krjaskowiak25/T41-SDT-Published/V010 5 in case Stl Files/T41 stand V010-Body.stl

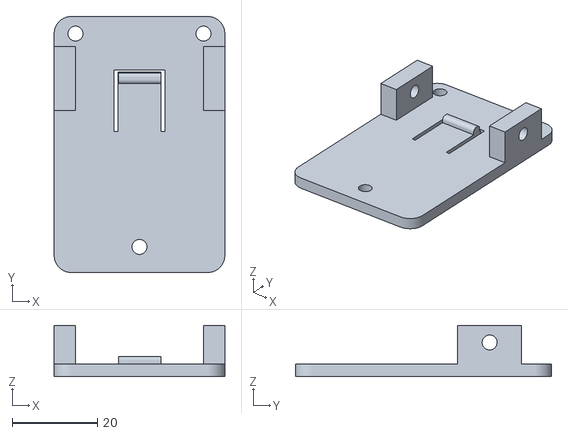
[picture p15: CAD file, 2022-06-29]
V010 5 in case Stl Files/T41 stand V010-Body.stl
40.0 x 60.0 x 12.0
