krjaskowiak25/T41-SDT-Published/V011 7 in case files/T41 7in Side Right Panel V011.FCStd

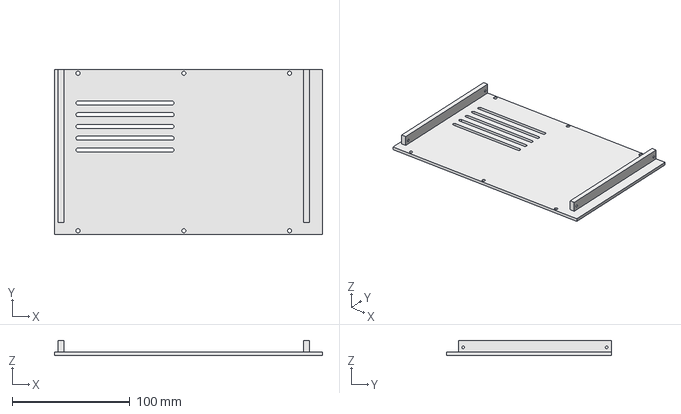
[picture p16: CAD file, 2022-06-29]
V011 7 in case files/T41 7in Side Right Panel V011.FCStd
228.0 x 140.0 x 13.0 mm
