krjaskowiak25/T41-SDT-Published/V011 7 in case files/T41 7in Base Left  V011.FCStd

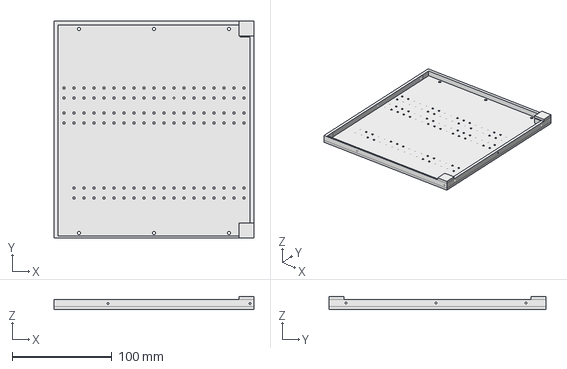
[picture p17: CAD file, 2022-06-29]
V011 7 in case files/T41 7in Base Left V011.FCStd
200.0 x 217.0 x 13.0 mm
