krjaskowiak25/T41-SDT-Published/V010 5 in case FreeCad Files/T41 Back Right Panel V010.FCStd

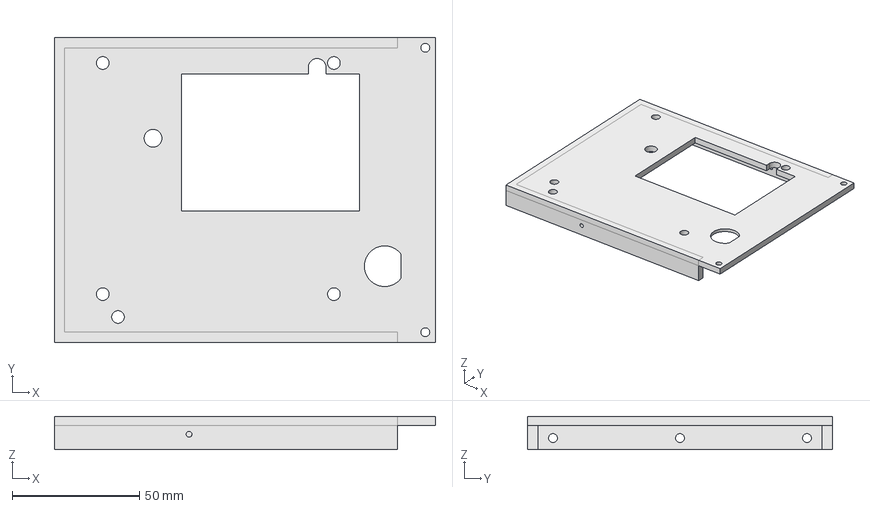
[picture p18: CAD file, 2022-06-29]
V010 5 in case FreeCad Files/T41 Back Right Panel V010.FCStd
150.0 x 120.0 x 13.0 mm
