krjaskowiak25/T41-SDT-Published/V011 7 in case files/T41 7in Front left panelV011.FCStd

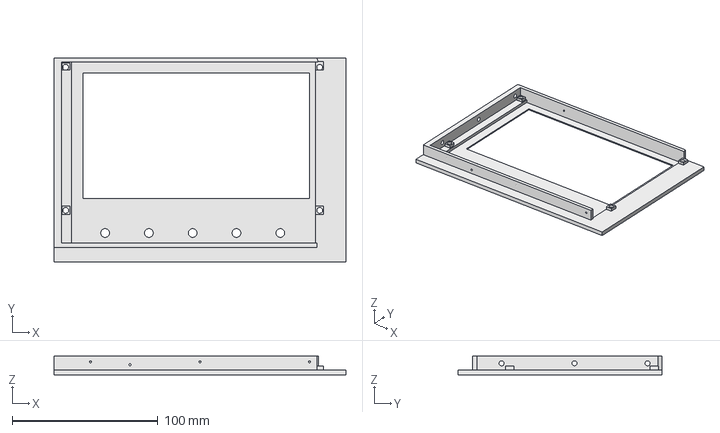
[picture p19: CAD file, 2022-06-29]
V011 7 in case files/T41 7in Front left panelV011.FCStd
200.0 x 140.0 x 13.0 mm
