krjaskowiak25/T41-SDT-Published/V011 7 in case files/T41 7IN Front Right Panel V011.FCStd

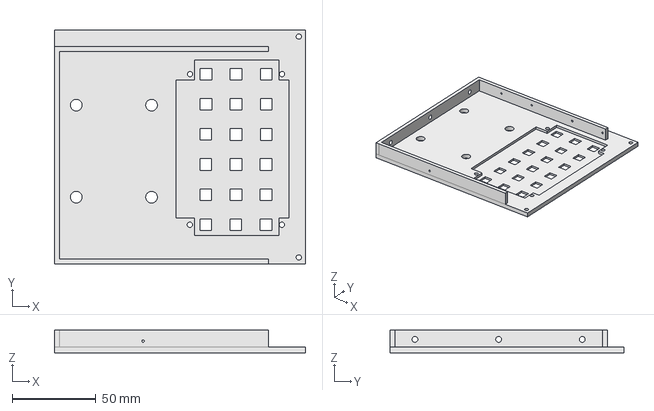
[picture p20: CAD file, 2022-06-29]
V011 7 in case files/T41 7IN Front Right Panel V011.FCStd
150.0 x 140.0 x 13.5 mm
