krjaskowiak25/T41-SDT-Published/V011 7 in case files/T41 7in Top Left Panel Speaker Vents V011.FCStd

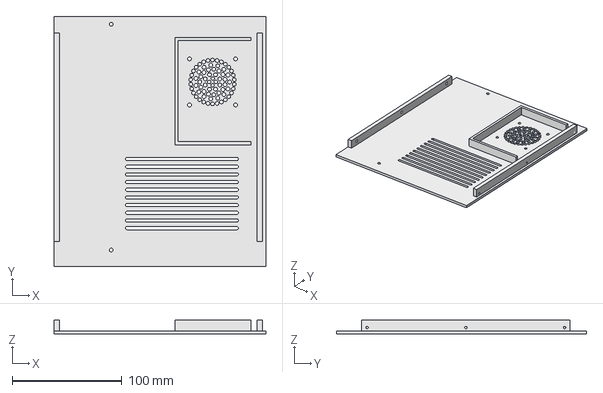
[picture p22: CAD file, 2022-06-29]
V011 7 in case files/T41 7in Top Left Panel Speaker Vents V011.FCStd
193.0 x 228.0 x 13.0 mm
